svddevelop/techtool/img/orig/config.single.txt

dtparam=spi=on
dtoverlay=mcp2515-can0,oscillator=8000000,interrupt=25
dtoverlay=spi-bcm2835-overlay
dtoverlay=dwc2
